helen-bovington/analog_music_synth/schematics_and_waveforms/SUSTAIN_waveform.png

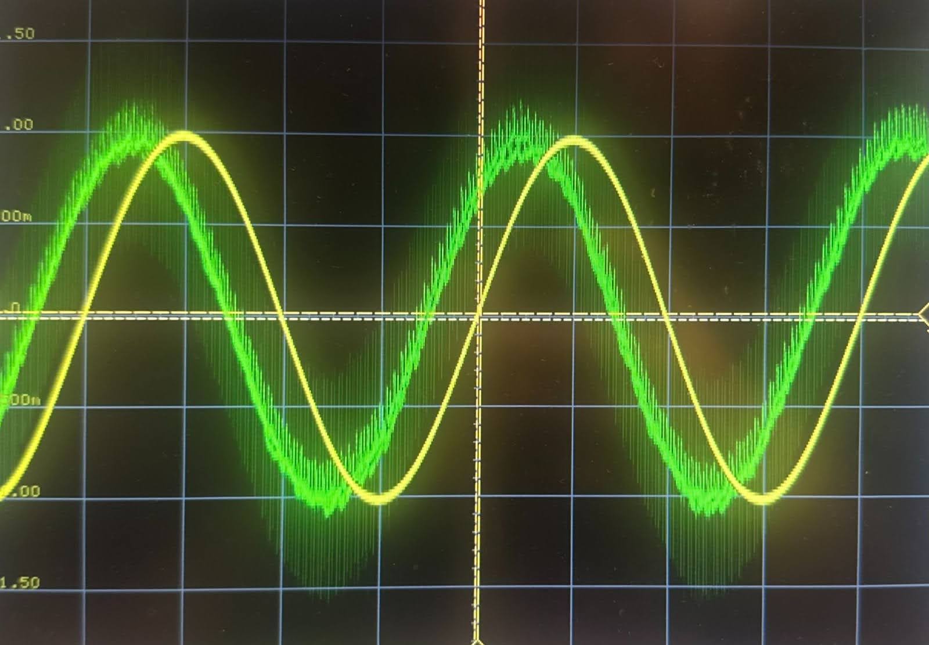
schematics_and_waveforms/SUSTAIN_waveform.png
