helen-bovington/analog_music_synth/analog_synth_block_diagram.png

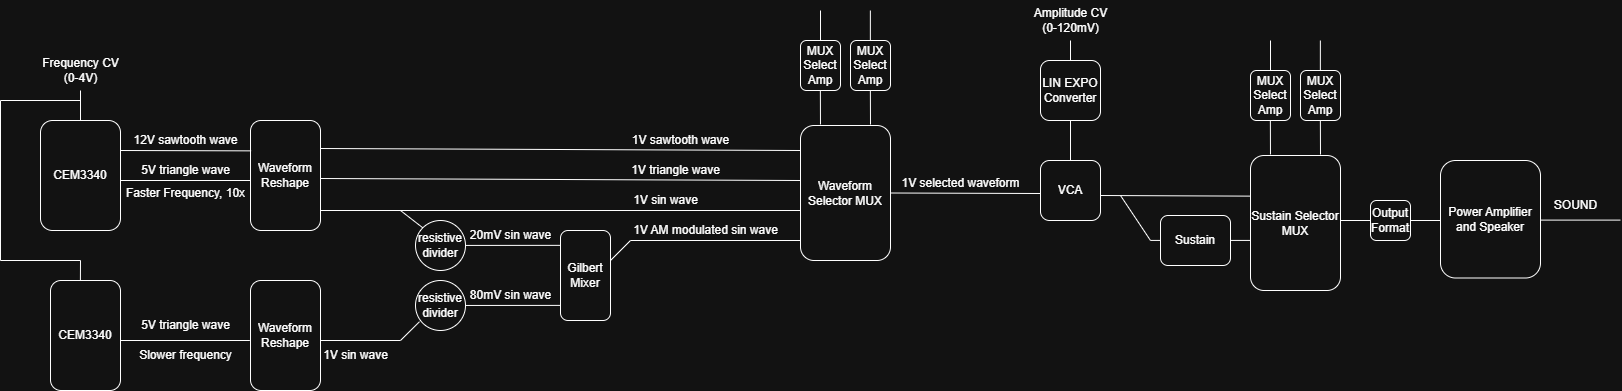
analog_synth_block_diagram.png
