helen-bovington/analog_music_synth/Cadence_files/2N2222/symbol/thumbnail_128x128.png

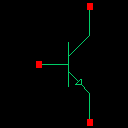
Cadence_files/2N2222/symbol/thumbnail_128x128.png
