helen-bovington/analog_music_synth/Cadence_files/3_8_DECODE/schematic/thumbnail_128x128.png

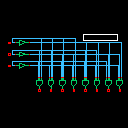
Cadence_files/3_8_DECODE/schematic/thumbnail_128x128.png
