helen-bovington/analog_music_synth/Cadence_files/3AND/symbol/thumbnail_128x128.png

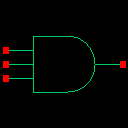
Cadence_files/3AND/symbol/thumbnail_128x128.png
