helen-bovington/analog_music_synth/Cadence_files/20mV_DIV/schematic/thumbnail_128x128.png

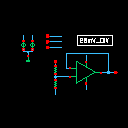
Cadence_files/20mV_DIV/schematic/thumbnail_128x128.png
