helen-bovington/analog_music_synth/Cadence_files/20mV_DIV/symbol/thumbnail_128x128.png

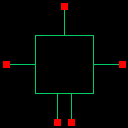
Cadence_files/20mV_DIV/symbol/thumbnail_128x128.png
