helen-bovington/analog_music_synth/Cadence_files/ADG5082/schematic/thumbnail_128x128.png

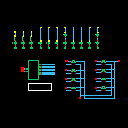
Cadence_files/ADG5082/schematic/thumbnail_128x128.png
