helen-bovington/analog_music_synth/Cadence_files/GILBERT/schematic/thumbnail_128x128.png

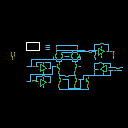
Cadence_files/GILBERT/schematic/thumbnail_128x128.png
