helen-bovington/analog_music_synth/Cadence_files/GILBERT/symbol/thumbnail_128x128.png

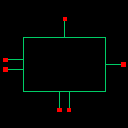
Cadence_files/GILBERT/symbol/thumbnail_128x128.png
