helen-bovington/analog_music_synth/Cadence_files/LF411/symbol/thumbnail_128x128.png

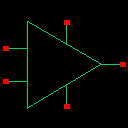
Cadence_files/LF411/symbol/thumbnail_128x128.png
