helen-bovington/analog_music_synth/Cadence_files/MUX_SELECT_AMPLIFIER/schematic/thumbnail_128x128.png

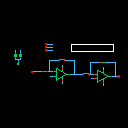
Cadence_files/MUX_SELECT_AMPLIFIER/schematic/thumbnail_128x128.png
