helen-bovington/analog_music_synth/Cadence_files/OUT_PROC/schematic/thumbnail_128x128.png

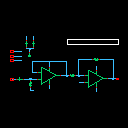
Cadence_files/OUT_PROC/schematic/thumbnail_128x128.png
