helen-bovington/analog_music_synth/Cadence_files/VCA/schematic/thumbnail_128x128.png

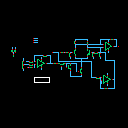
Cadence_files/VCA/schematic/thumbnail_128x128.png
