helen-bovington/analog_music_synth/Cadence_files/VCA/symbol/thumbnail_128x128.png

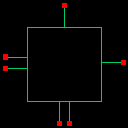
Cadence_files/VCA/symbol/thumbnail_128x128.png
