helen-bovington/analog_music_synth/Cadence_files/WAVE_RESHAPE/schematic/thumbnail_128x128.png

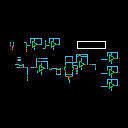
Cadence_files/WAVE_RESHAPE/schematic/thumbnail_128x128.png
