helen-bovington/analog_music_synth/schematics_and_waveforms/3_8_DECODE_Sch.png

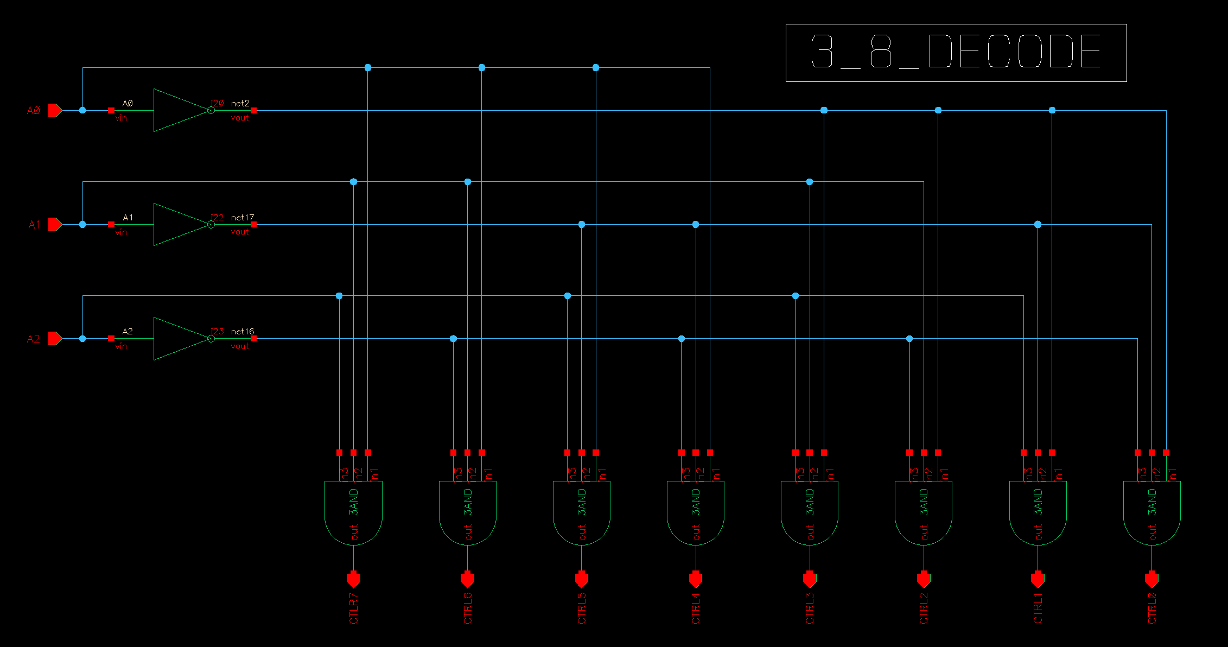
schematics_and_waveforms/3_8_DECODE_Sch.png
