helen-bovington/analog_music_synth/schematics_and_waveforms/3_8_DECODE_waveform.png

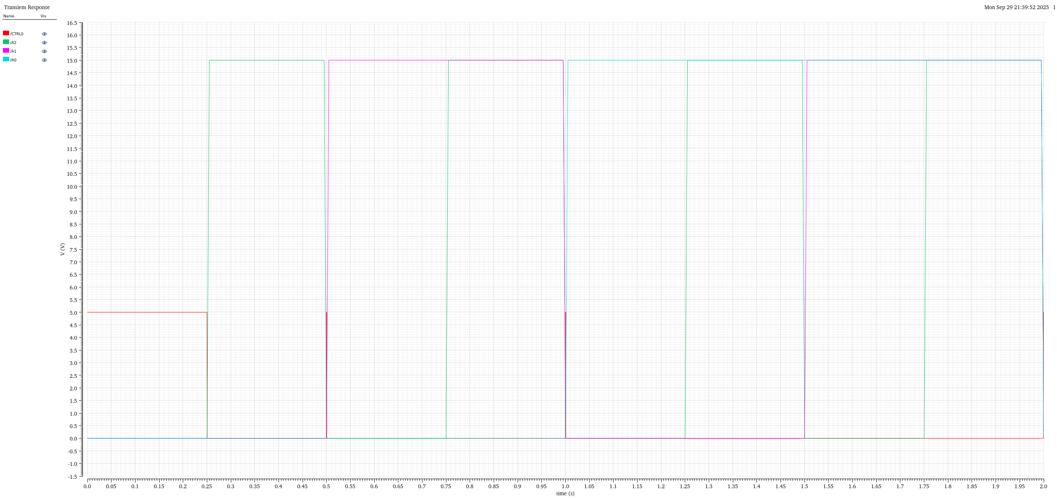
schematics_and_waveforms/3_8_DECODE_waveform.png
