helen-bovington/analog_music_synth/schematics_and_waveforms/20mV_DIV_Sch.png

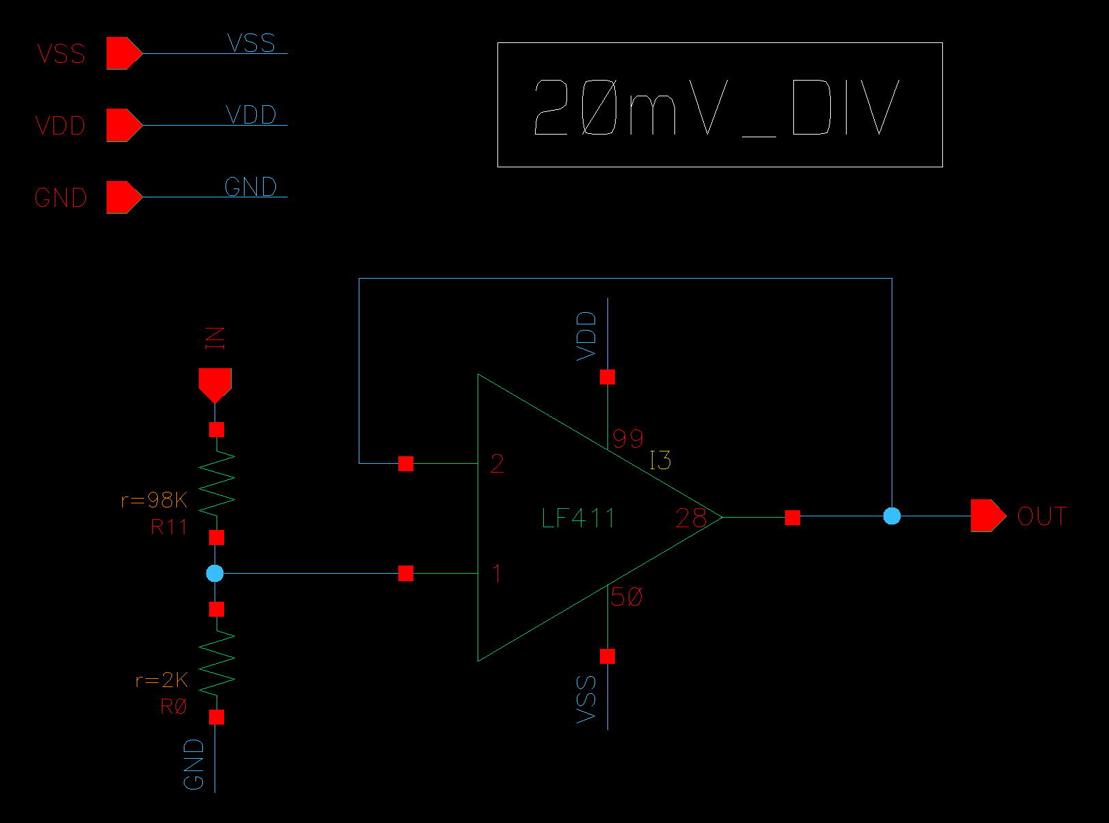
schematics_and_waveforms/20mV_DIV_Sch.png
