helen-bovington/analog_music_synth/schematics_and_waveforms/80mV_DIV_waveform.png

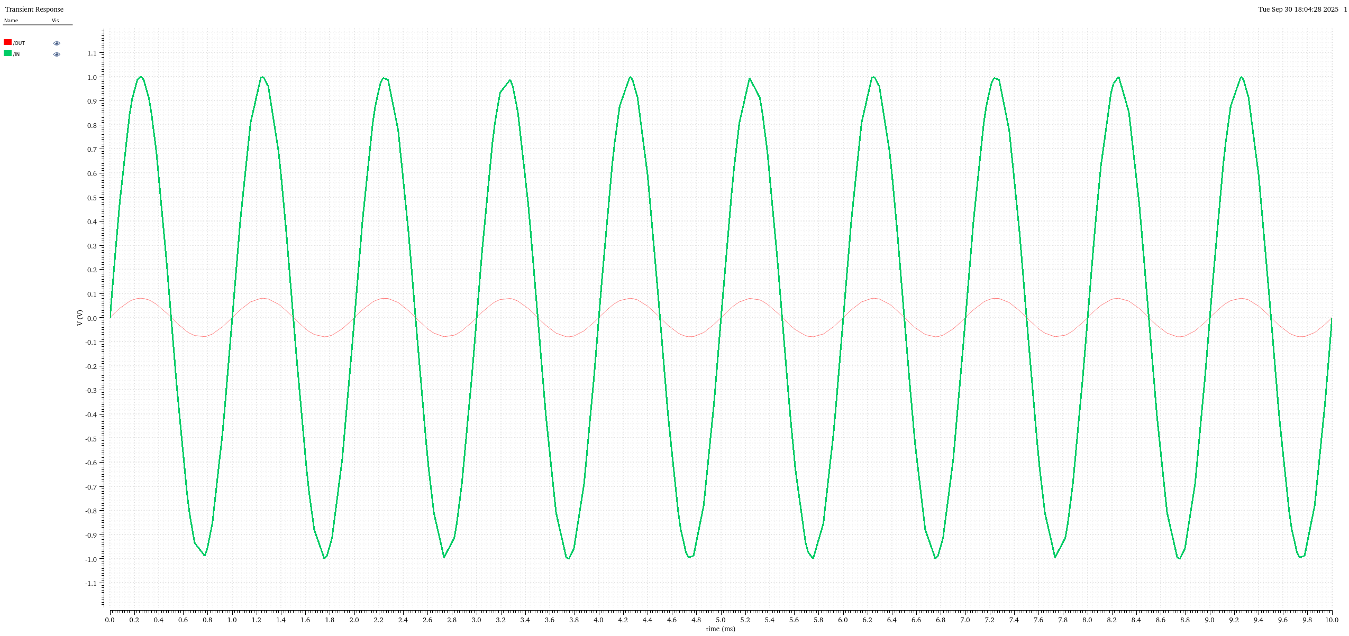
schematics_and_waveforms/80mV_DIV_waveform.png
