helen-bovington/analog_music_synth/schematics_and_waveforms/ADG5082_waveform.png

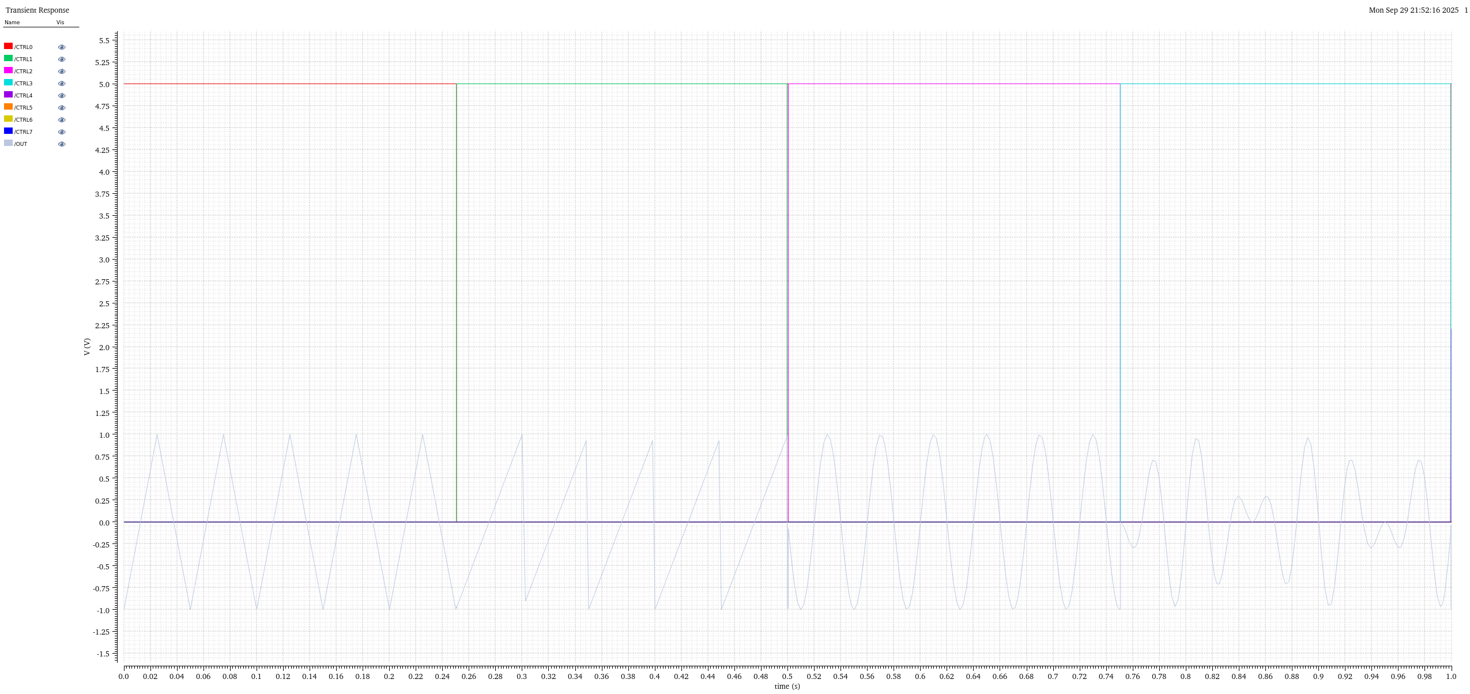
schematics_and_waveforms/ADG5082_waveform.png
