helen-bovington/analog_music_synth/schematics_and_waveforms/FULL_INTEGRATION1.png

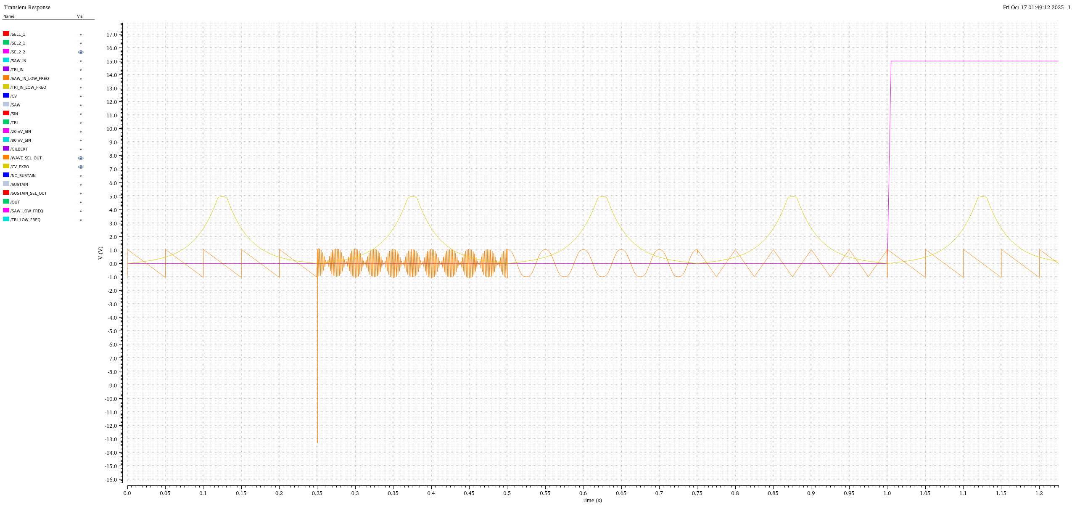
schematics_and_waveforms/FULL_INTEGRATION1.png
