helen-bovington/analog_music_synth/schematics_and_waveforms/FULL_INTEGRATION2.png

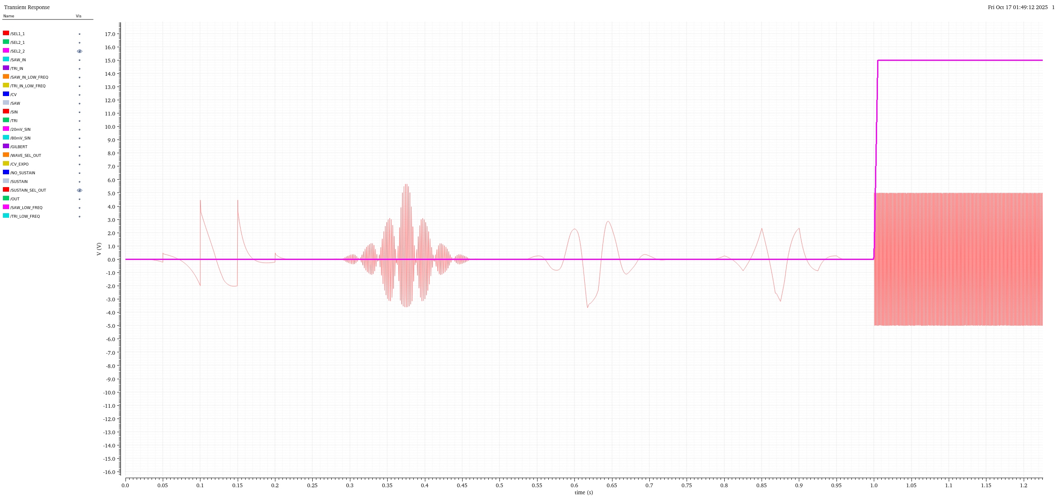
schematics_and_waveforms/FULL_INTEGRATION2.png
