helen-bovington/analog_music_synth/schematics_and_waveforms/FULL_INTEGRATION3.png

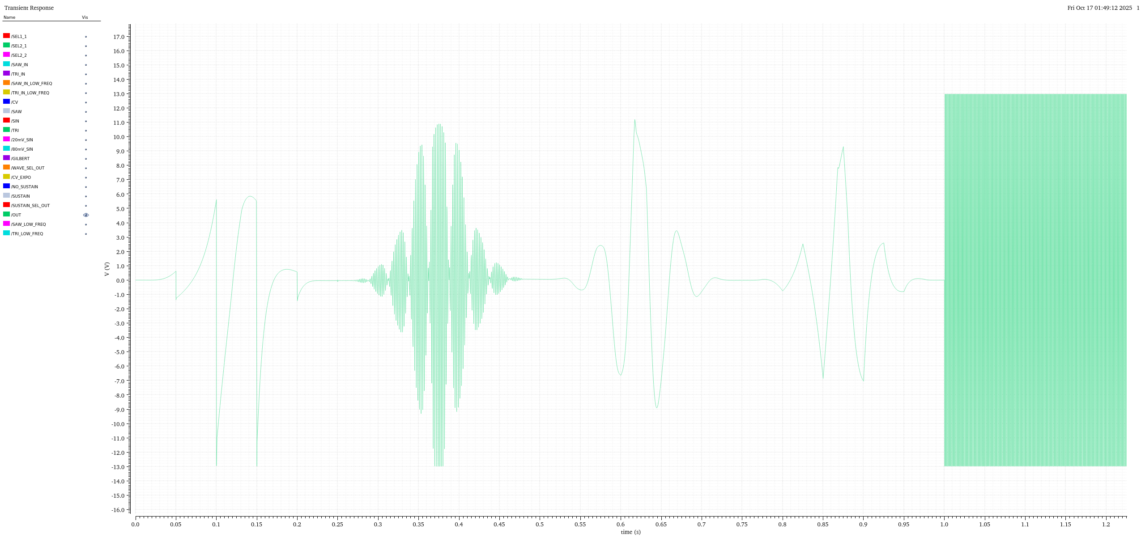
schematics_and_waveforms/FULL_INTEGRATION3.png
