helen-bovington/analog_music_synth/schematics_and_waveforms/FULL_INTEGRATION.png

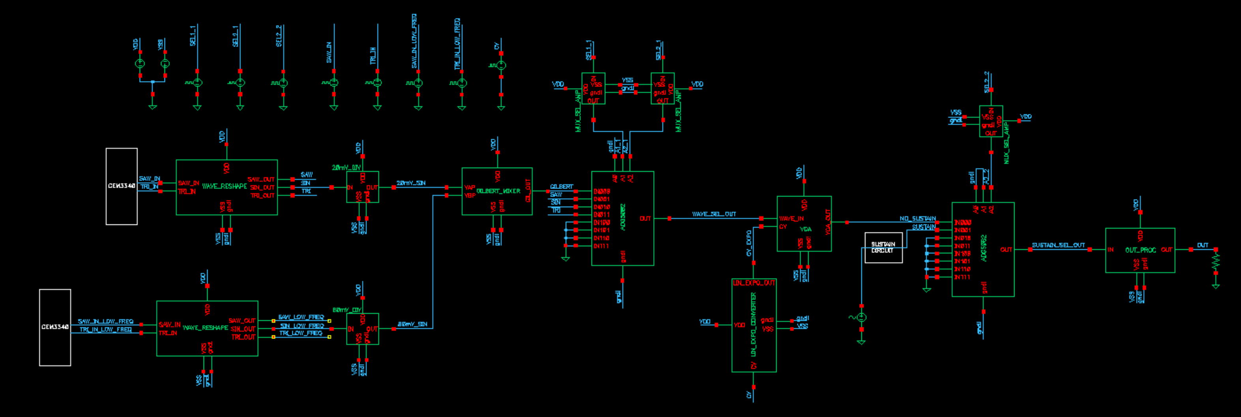
schematics_and_waveforms/FULL_INTEGRATION.png
