helen-bovington/analog_music_synth/schematics_and_waveforms/GILBERT_MIXER_Sch.png

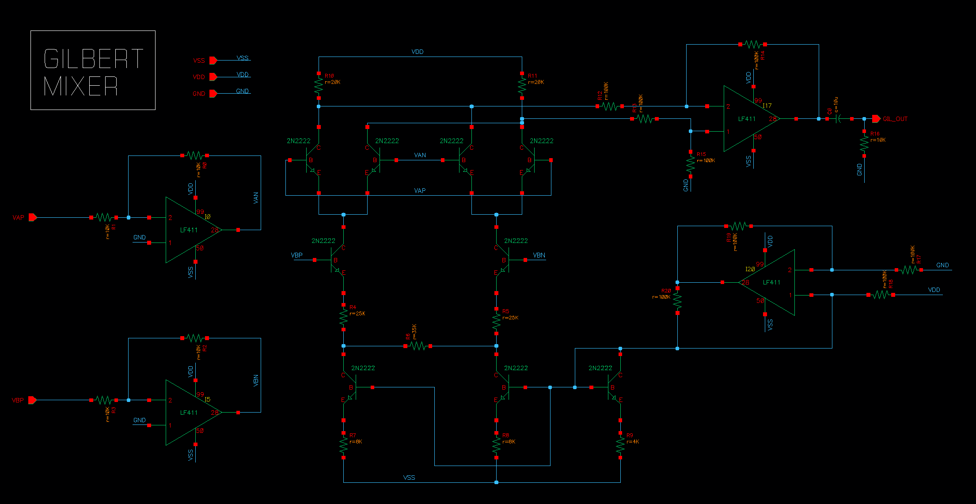
schematics_and_waveforms/GILBERT_MIXER_Sch.png
