helen-bovington/analog_music_synth/schematics_and_waveforms/GILBERT_MIXER_waveform.png

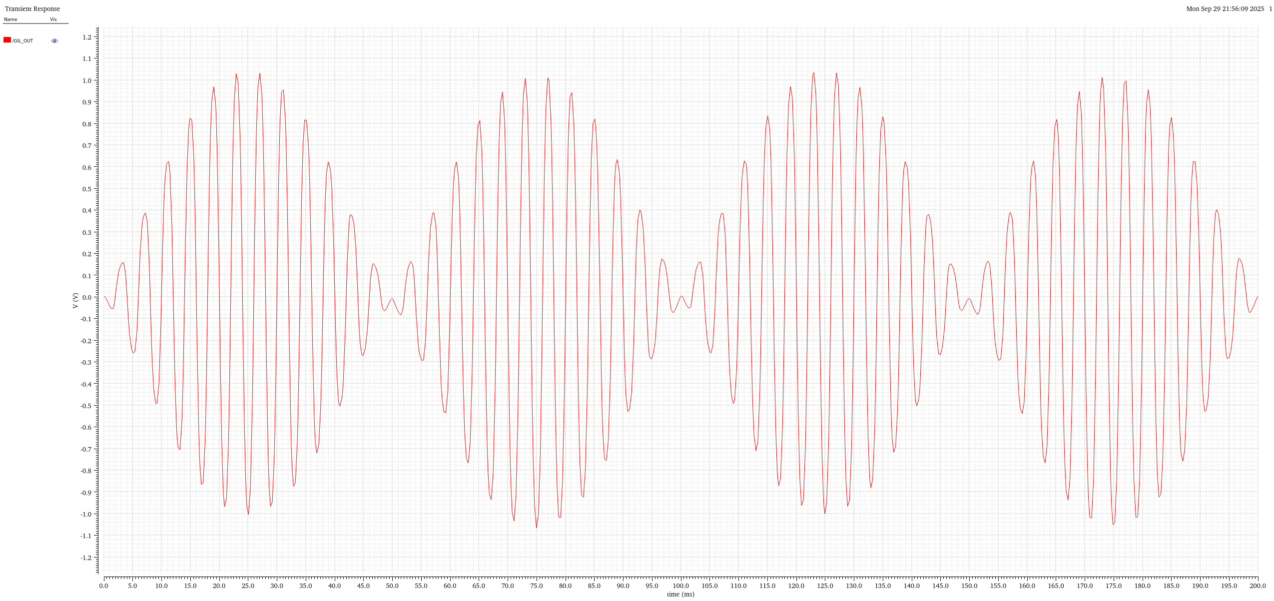
schematics_and_waveforms/GILBERT_MIXER_waveform.png
