helen-bovington/analog_music_synth/schematics_and_waveforms/LIN_EXPO_CONVERTER_Sch.png

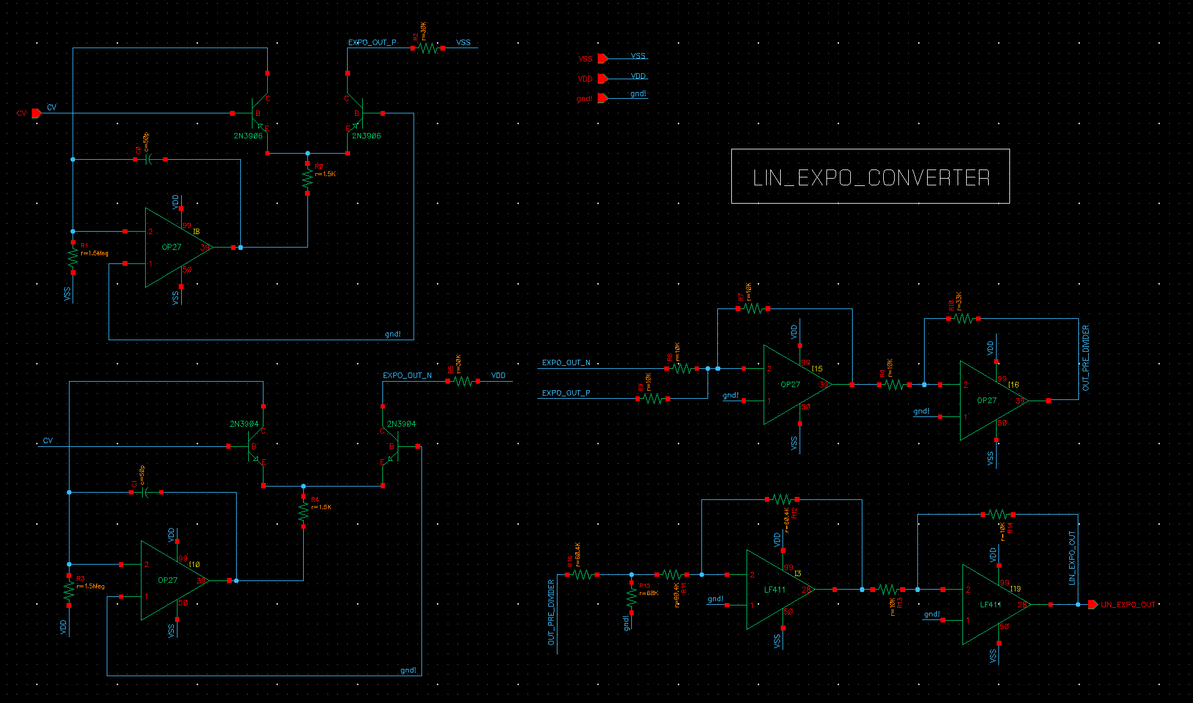
schematics_and_waveforms/LIN_EXPO_CONVERTER_Sch.png
