helen-bovington/analog_music_synth/schematics_and_waveforms/MUX_SELECT_AMP_Sch.png

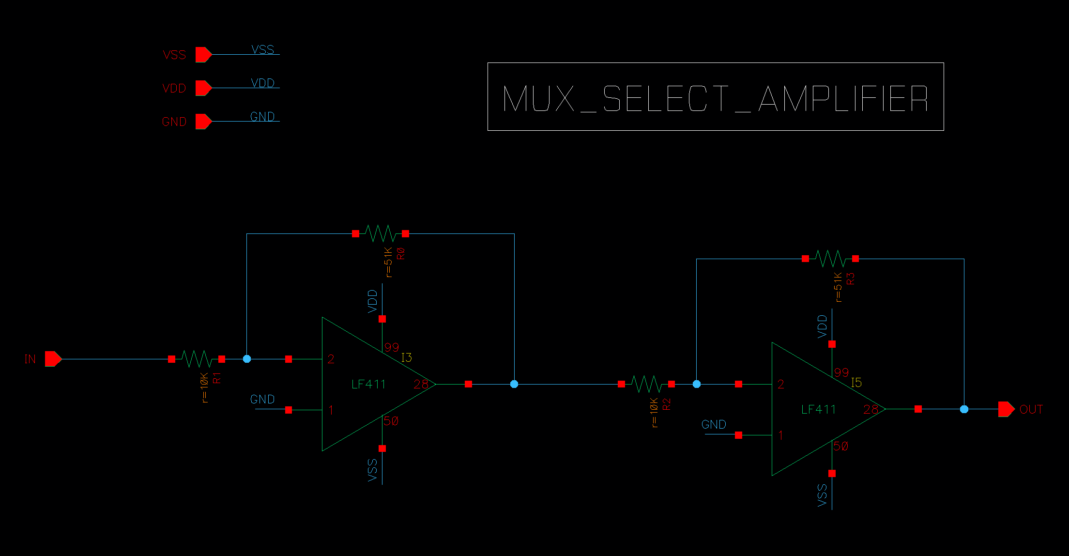
schematics_and_waveforms/MUX_SELECT_AMP_Sch.png
