helen-bovington/analog_music_synth/schematics_and_waveforms/MUX_SELECT_AMP_waveform.png

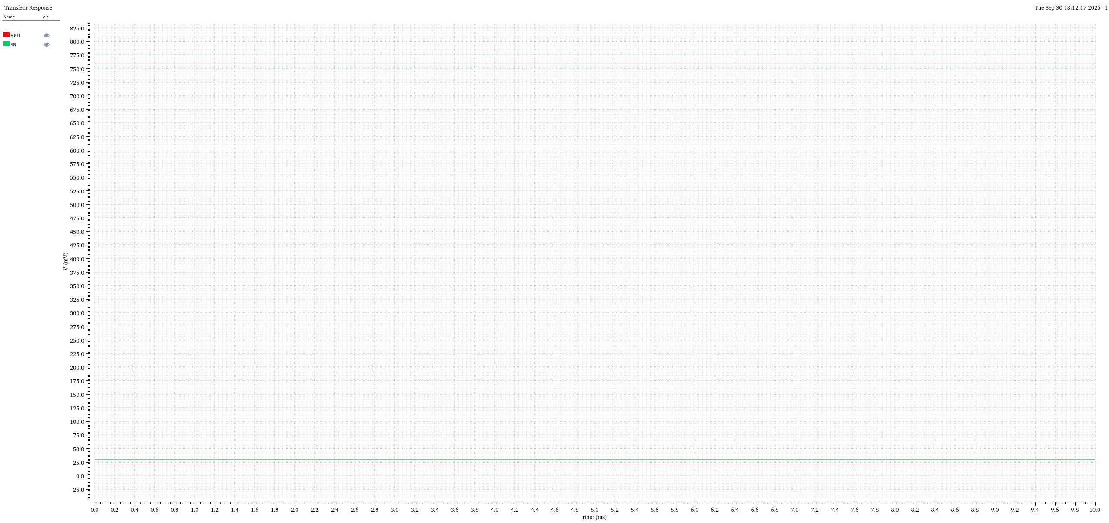
schematics_and_waveforms/MUX_SELECT_AMP_waveform.png
