helen-bovington/analog_music_synth/schematics_and_waveforms/OUT_PROC_Sch.png

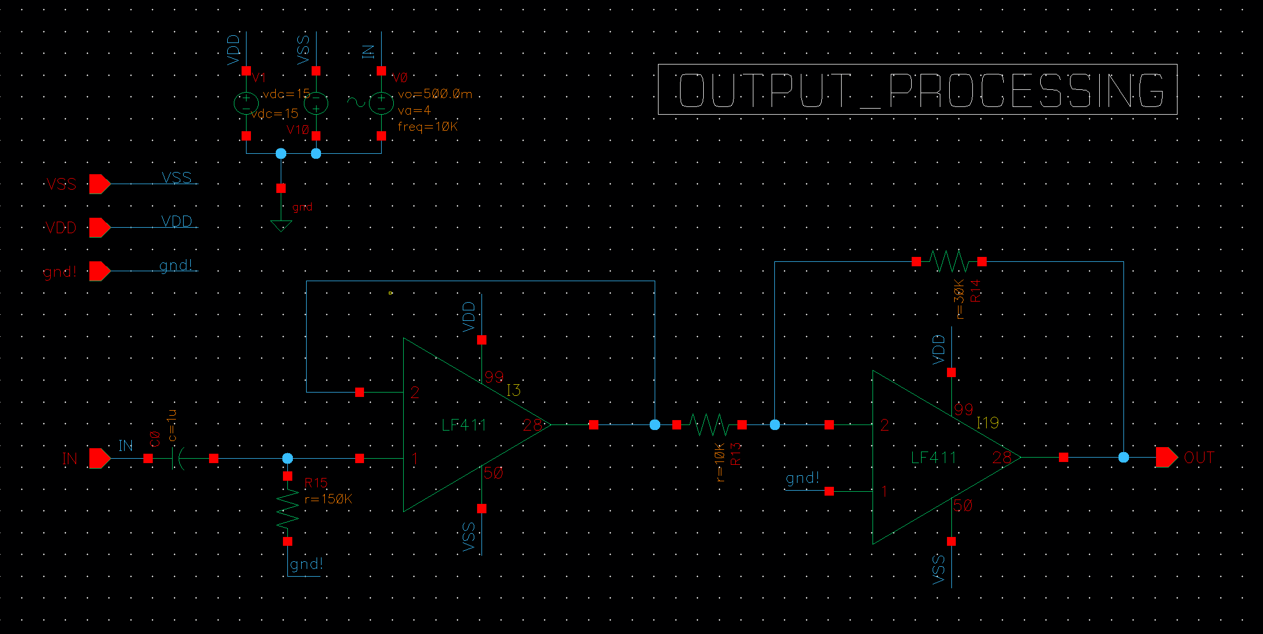
schematics_and_waveforms/OUT_PROC_Sch.png
