helen-bovington/analog_music_synth/schematics_and_waveforms/OUT_PROC_waveform.png

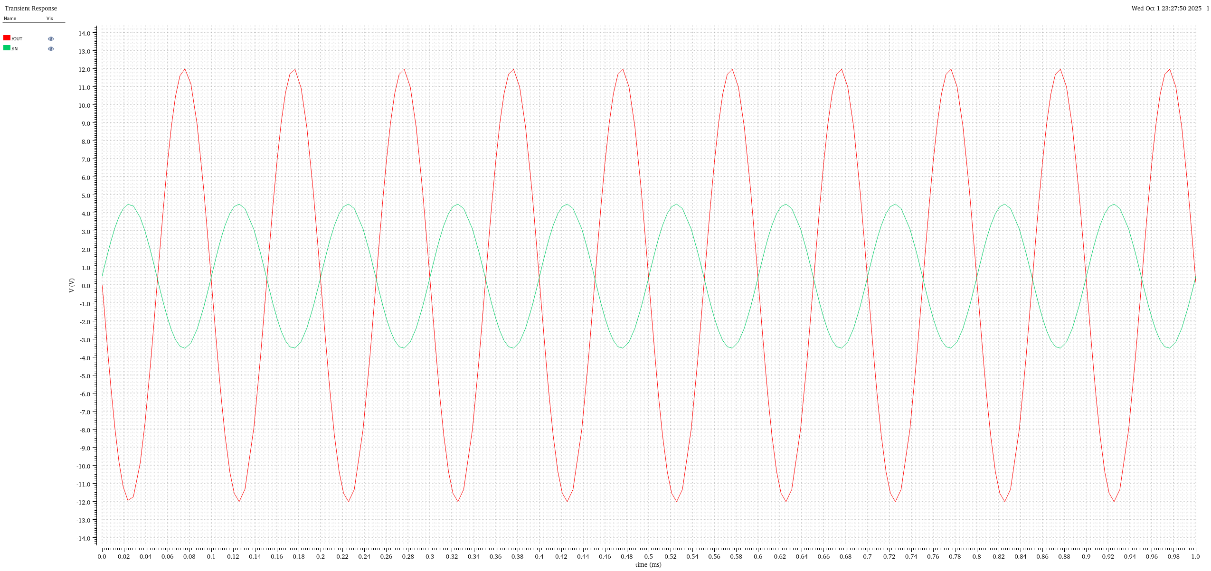
schematics_and_waveforms/OUT_PROC_waveform.png
