helen-bovington/analog_music_synth/schematics_and_waveforms/VCA_Sch.png

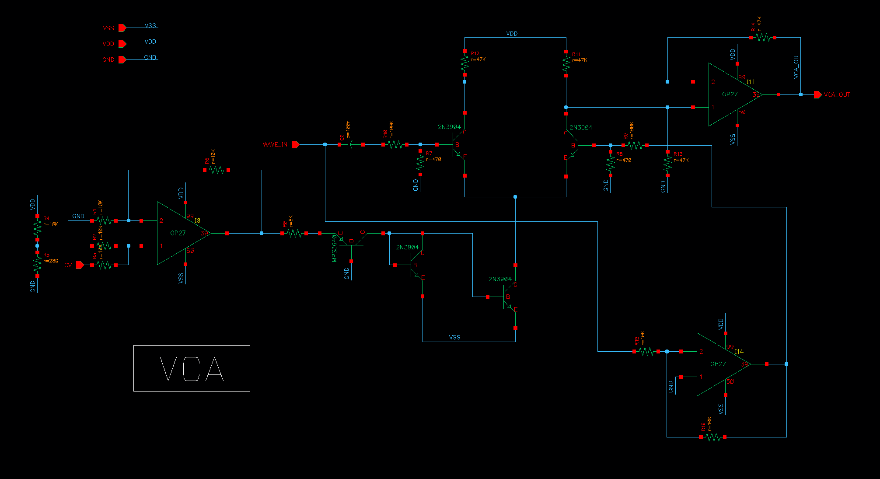
schematics_and_waveforms/VCA_Sch.png
