helen-bovington/analog_music_synth/schematics_and_waveforms/WAVE_RESHAPE_Sch.png

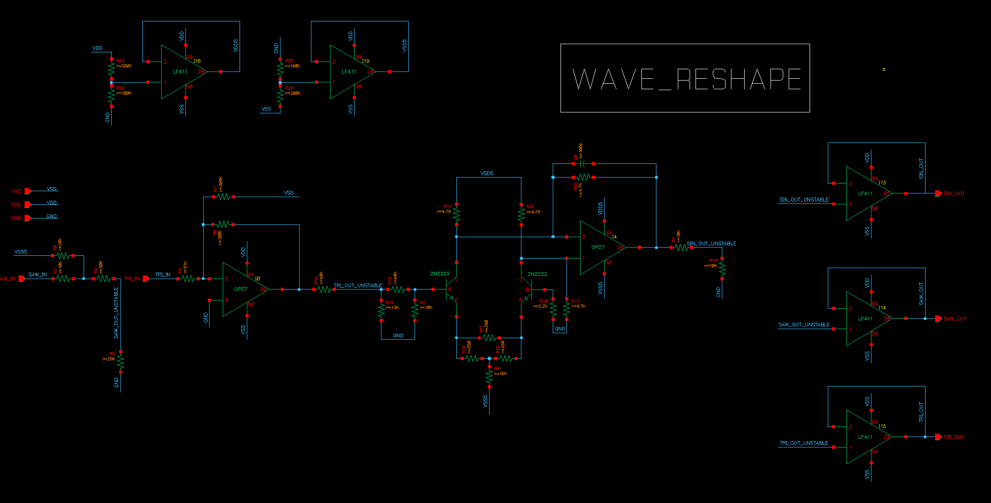
schematics_and_waveforms/WAVE_RESHAPE_Sch.png
