helen-bovington/analog_music_synth/schematics_and_waveforms/WAVE_RESHAPE_waveform.png

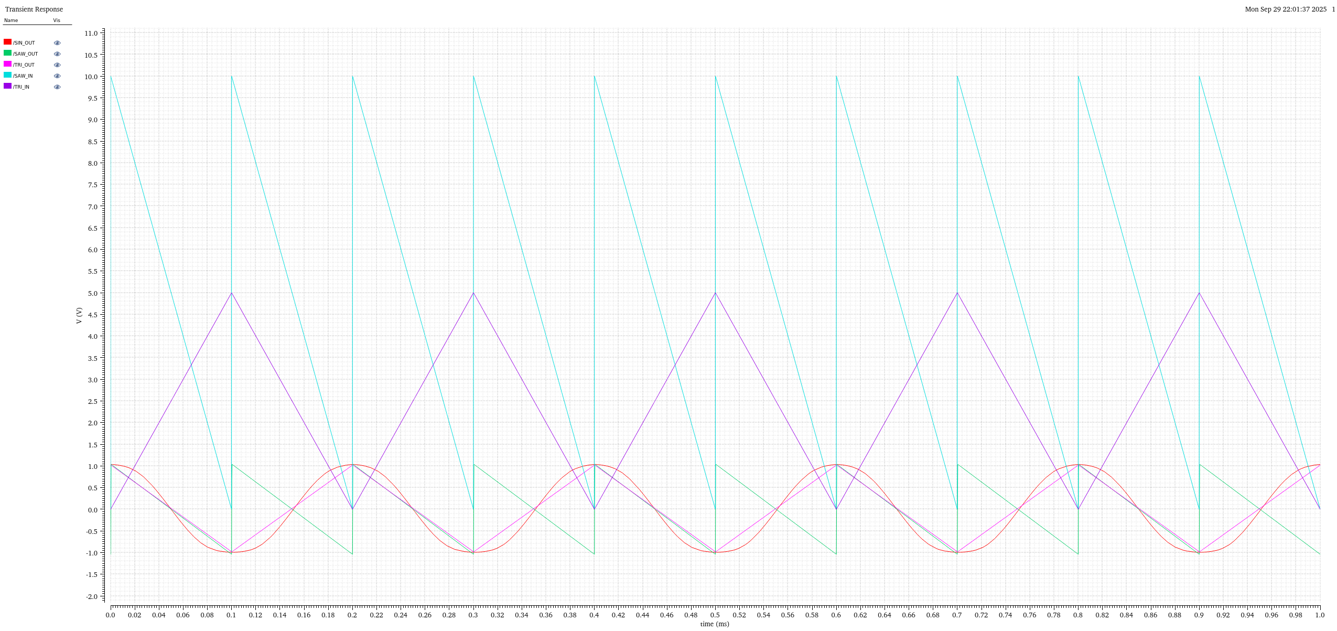
schematics_and_waveforms/WAVE_RESHAPE_waveform.png
